CoE-for-Smart-Production/mona/Images/20210218_104930.jpg

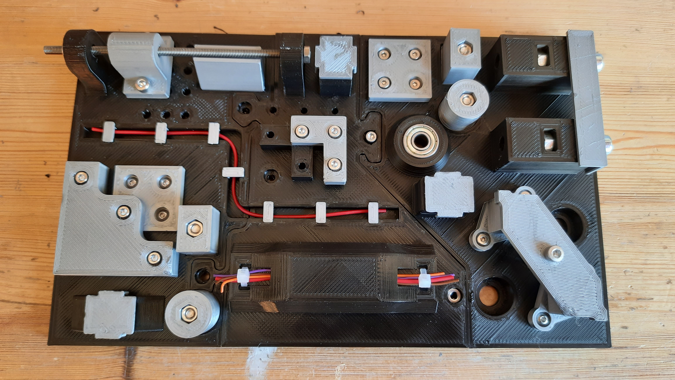
Images/20210218_104930.jpg
