CoE-for-Smart-Production/mona/Models/STL files/BL_Block.stl

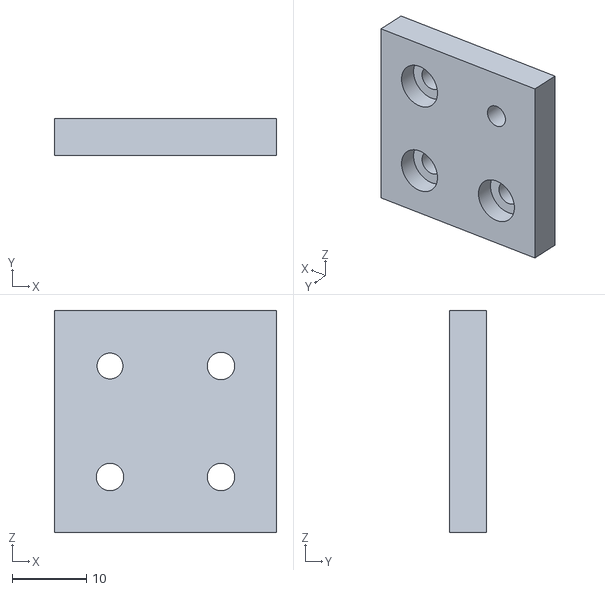
[picture p18: CAD file, 2021-03-04]
Models/STL files/BL_Block.stl
30.0 x 5.00 x 30.0
