CoE-for-Smart-Production/mona/Images/pre_evaluation_assembly.png

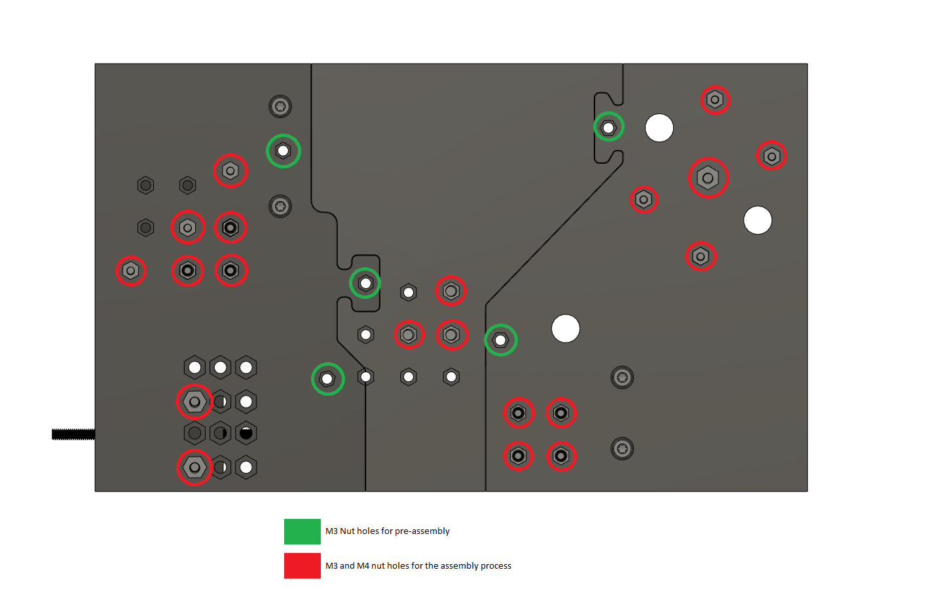
Images/pre_evaluation_assembly.png
