CoE-for-Smart-Production/mona/Images/Workinstruction/AS1_1.png

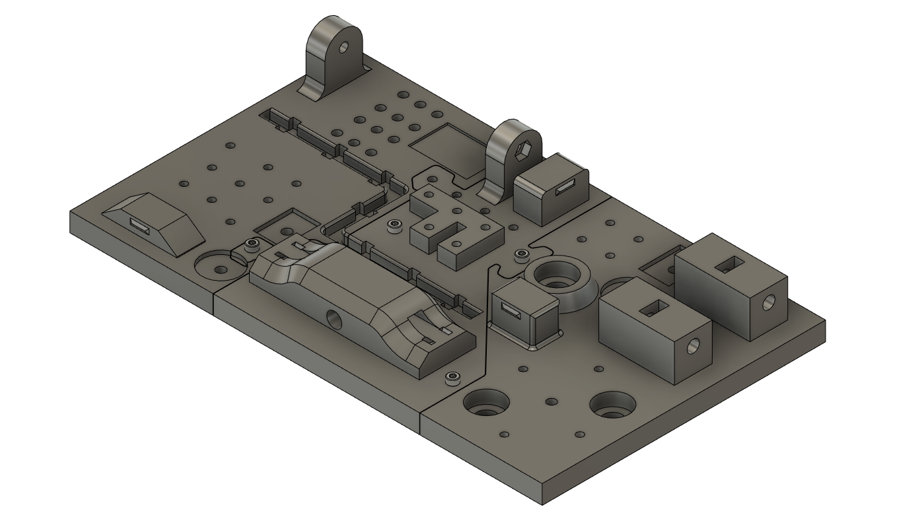
Images/Workinstruction/AS1_1.png
