CoE-for-Smart-Production/mona/Images/Workinstruction/AS2_1.png

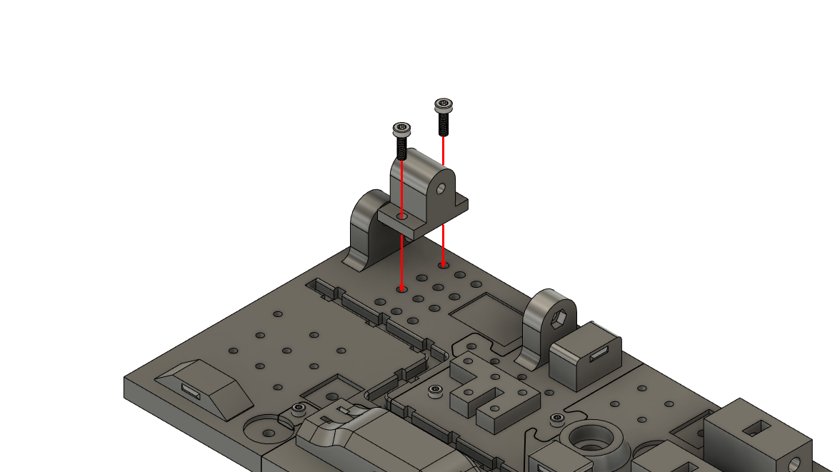
Images/Workinstruction/AS2_1.png
