CoE-for-Smart-Production/mona/Images/Workinstruction/AS2_2.png

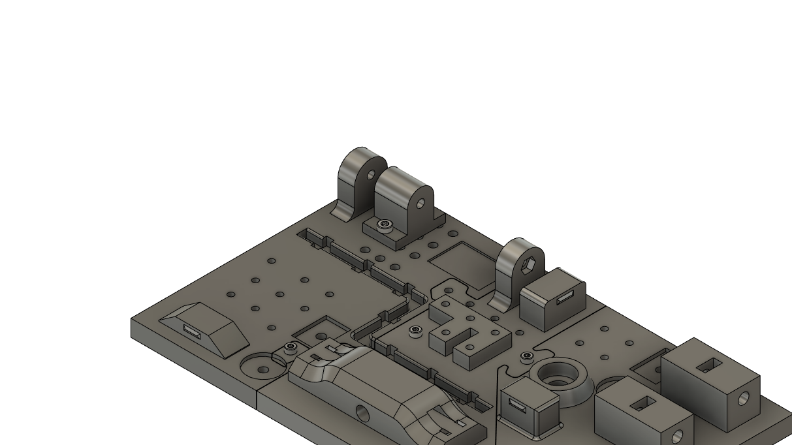
Images/Workinstruction/AS2_2.png
