CoE-for-Smart-Production/mona/Images/Workinstruction/AS3_1.png

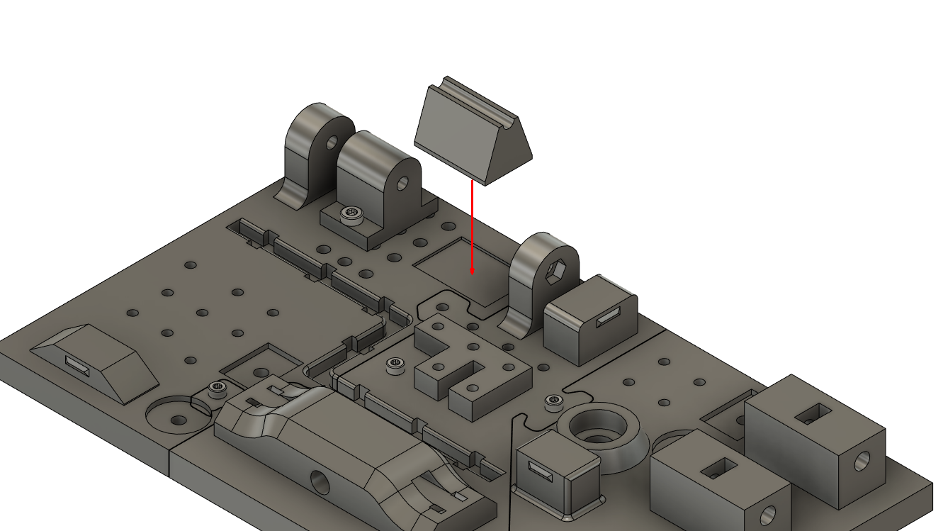
Images/Workinstruction/AS3_1.png
