CoE-for-Smart-Production/mona/Images/Workinstruction/AS3_2.png

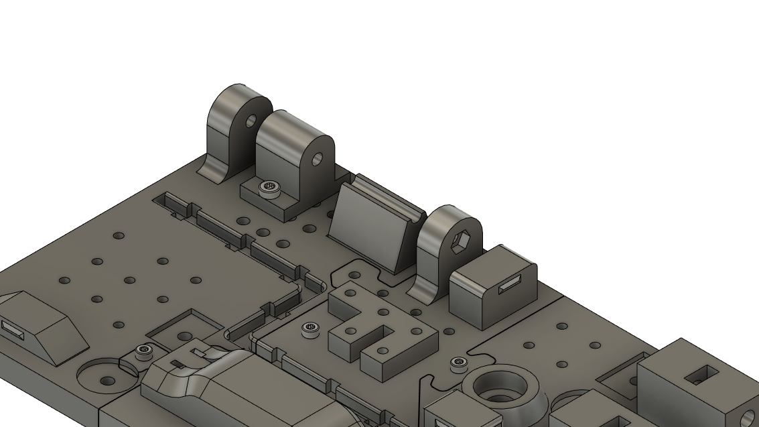
Images/Workinstruction/AS3_2.png
