CoE-for-Smart-Production/mona/Images/Workinstruction/AS4_2.png

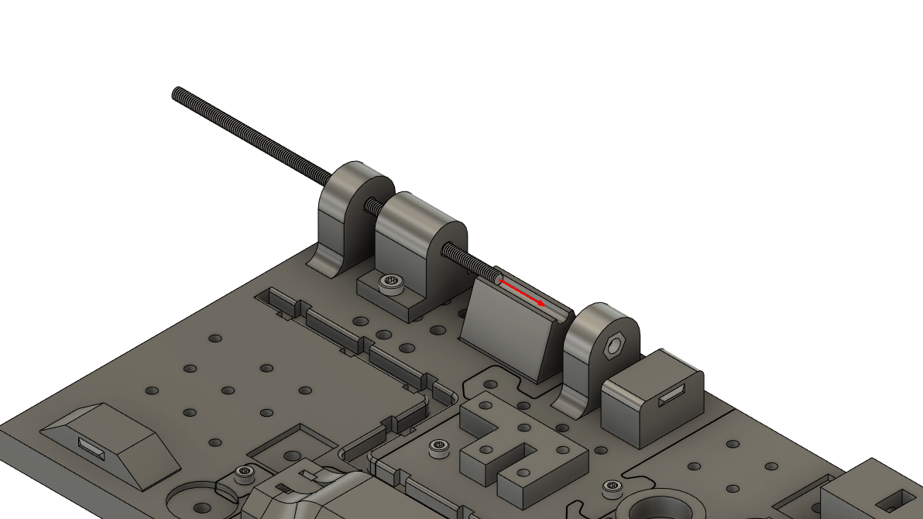
Images/Workinstruction/AS4_2.png
