CoE-for-Smart-Production/mona/Images/Workinstruction/AS4_3.png

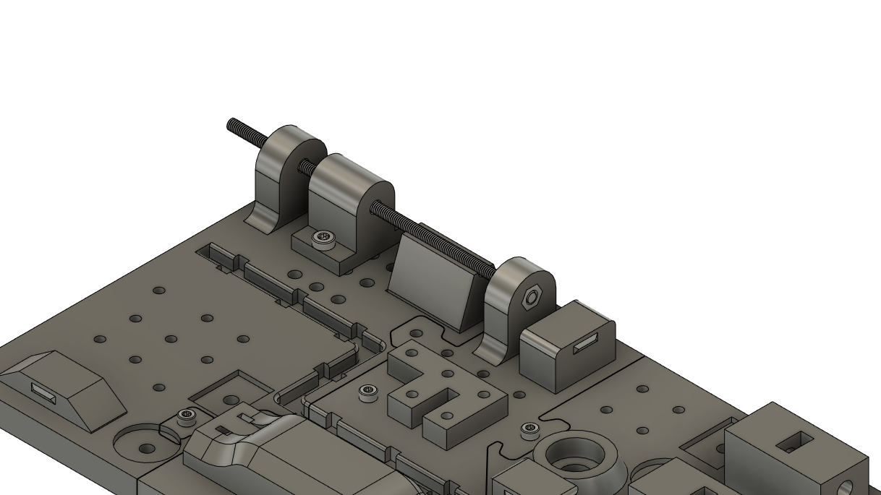
Images/Workinstruction/AS4_3.png
