CoE-for-Smart-Production/mona/Images/Workinstruction/AS5_1.png

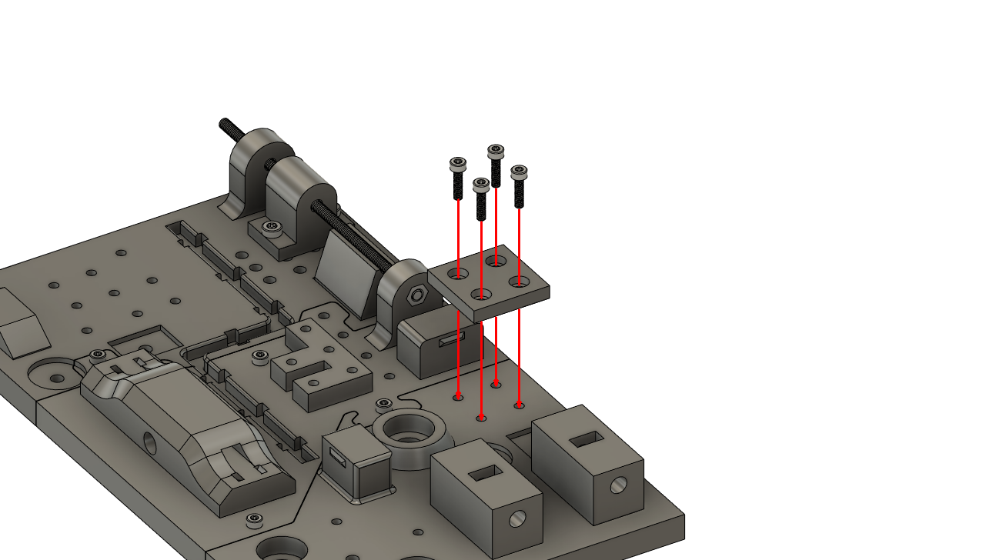
Images/Workinstruction/AS5_1.png
