CoE-for-Smart-Production/mona/Images/Workinstruction/AS5_2.png

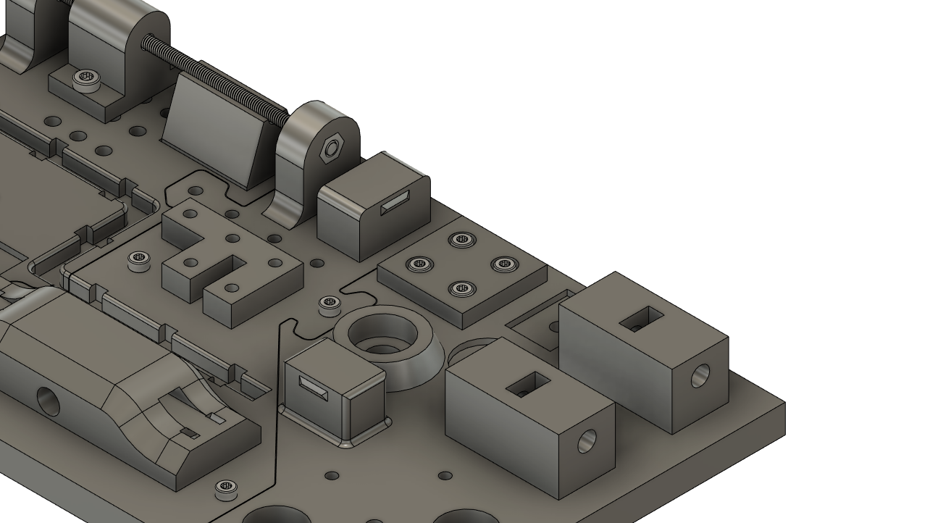
Images/Workinstruction/AS5_2.png
