CoE-for-Smart-Production/mona/Images/Workinstruction/AS6_1.png

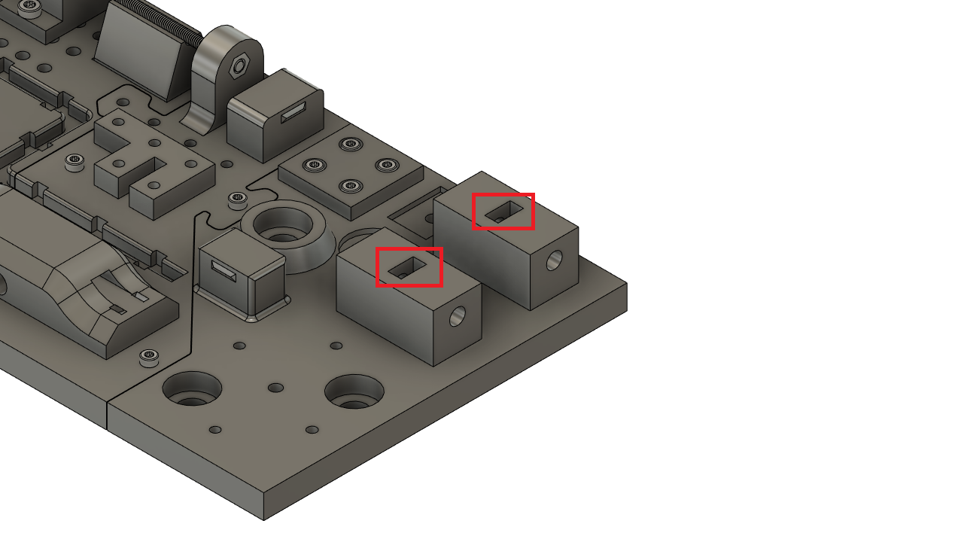
Images/Workinstruction/AS6_1.png
