CoE-for-Smart-Production/mona/Images/Workinstruction/AS6_2.png

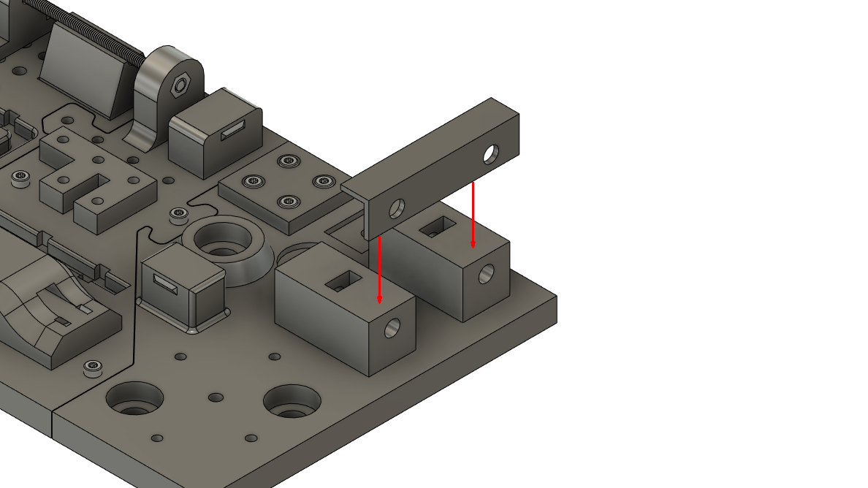
Images/Workinstruction/AS6_2.png
