CoE-for-Smart-Production/mona/Images/Workinstruction/AS6_3.png

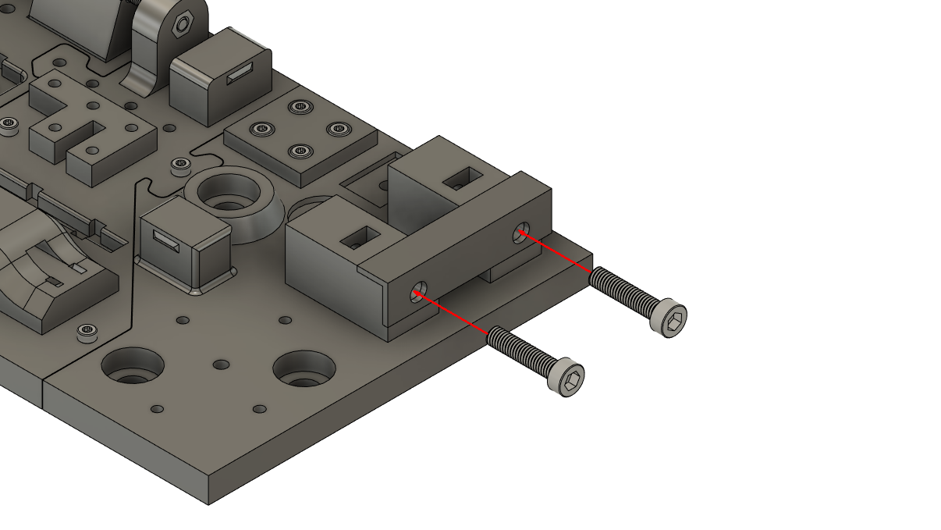
Images/Workinstruction/AS6_3.png
