CoE-for-Smart-Production/mona/Images/Workinstruction/AS7_1.png

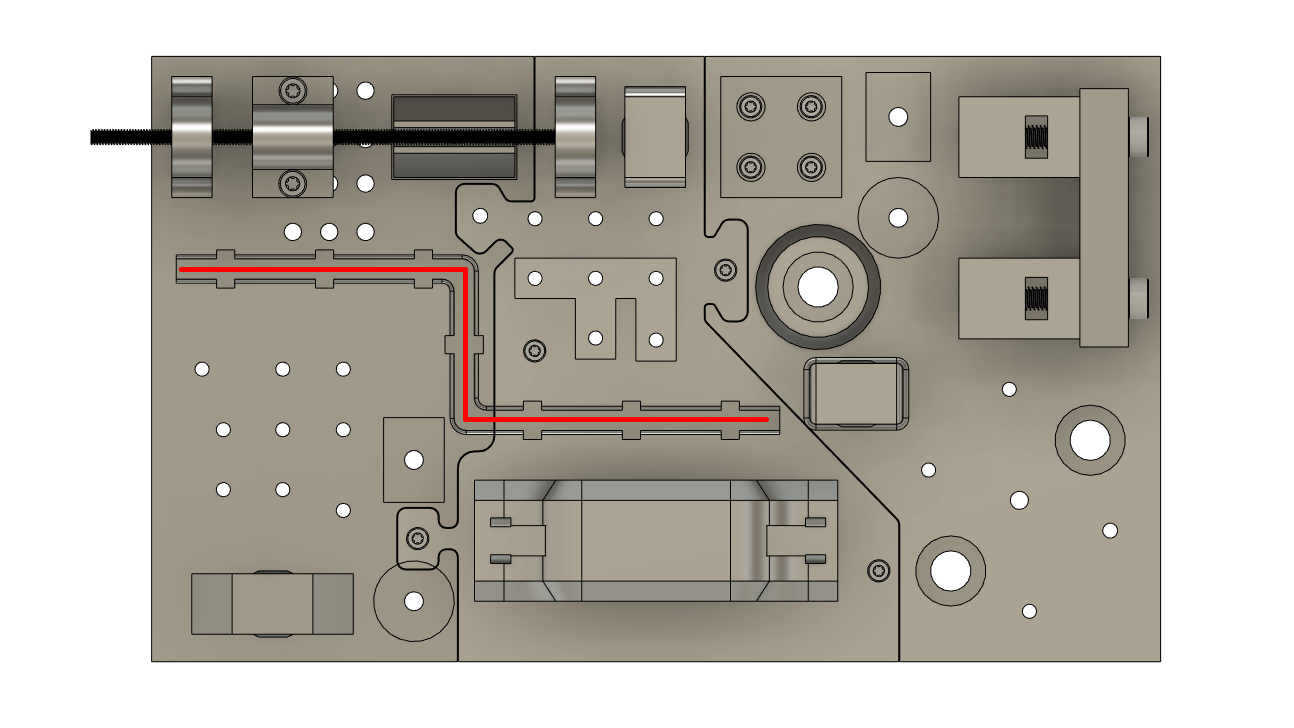
Images/Workinstruction/AS7_1.png
