CoE-for-Smart-Production/mona/Images/Workinstruction/AS7_2.png

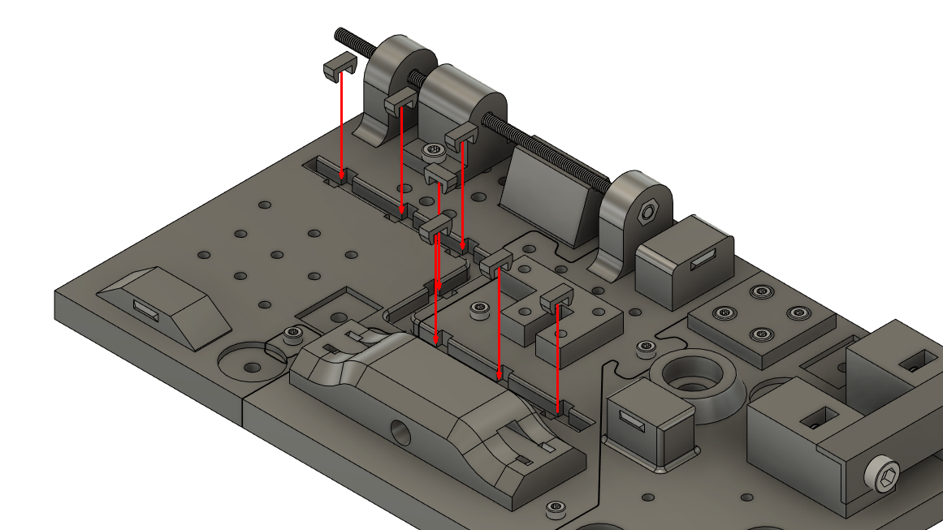
Images/Workinstruction/AS7_2.png
