CoE-for-Smart-Production/mona/Images/Workinstruction/AS7_3.png

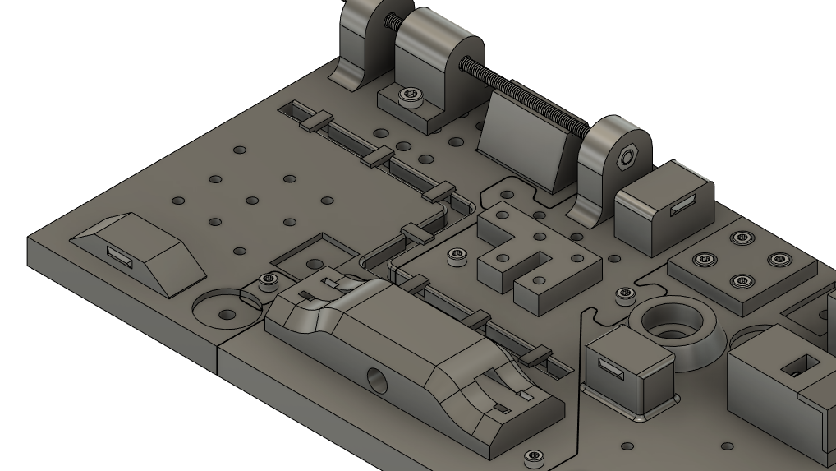
Images/Workinstruction/AS7_3.png
