CoE-for-Smart-Production/mona/Images/Workinstruction/AS8_1.png

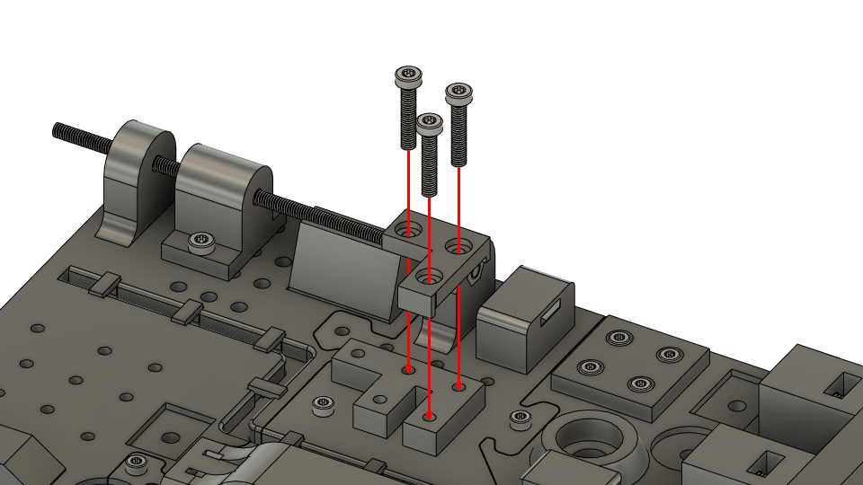
Images/Workinstruction/AS8_1.png
