CoE-for-Smart-Production/mona/Images/Workinstruction/AS8_2.png

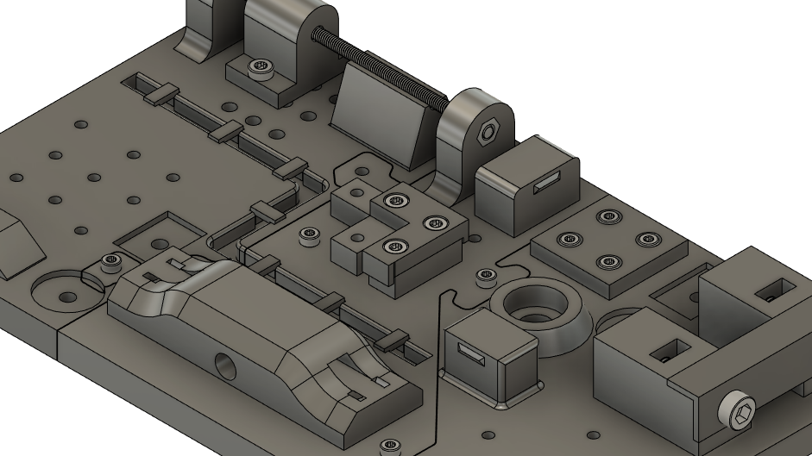
Images/Workinstruction/AS8_2.png
