CoE-for-Smart-Production/mona/Images/Workinstruction/AS9_1.png

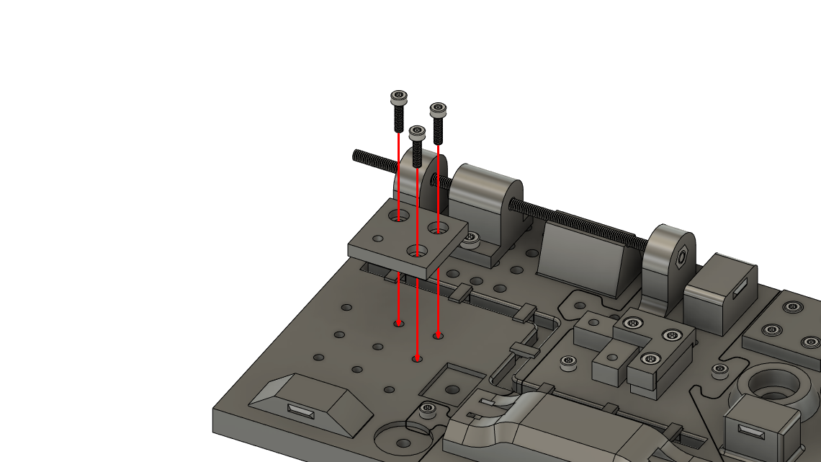
Images/Workinstruction/AS9_1.png
