CoE-for-Smart-Production/mona/Images/Workinstruction/AS9_2.png

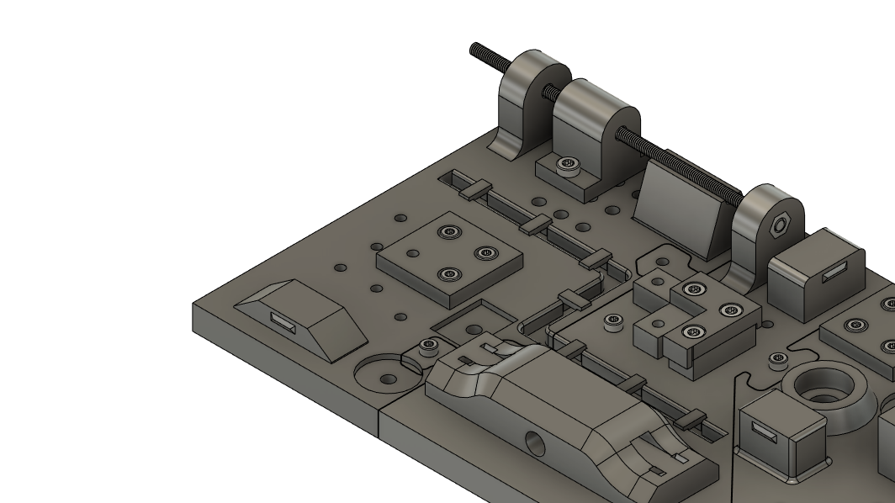
Images/Workinstruction/AS9_2.png
