CoE-for-Smart-Production/mona/Images/Workinstruction/AS10_1.png

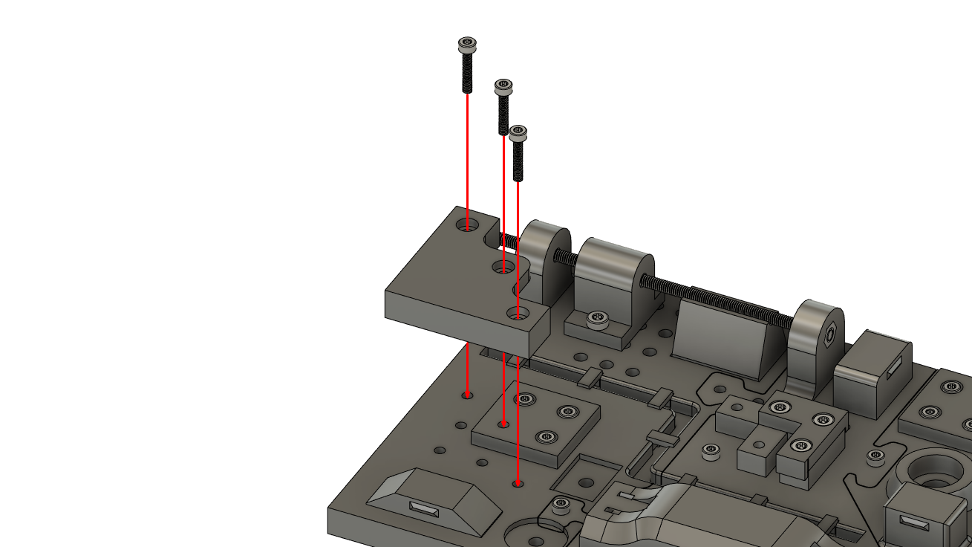
Images/Workinstruction/AS10_1.png
