CoE-for-Smart-Production/mona/Images/Workinstruction/AS10_2.png

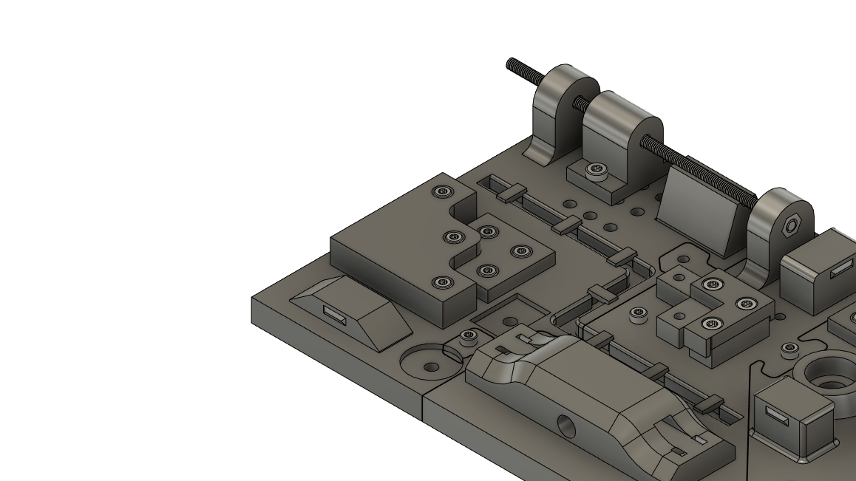
Images/Workinstruction/AS10_2.png
