CoE-for-Smart-Production/mona/Images/Workinstruction/AS11_3.png

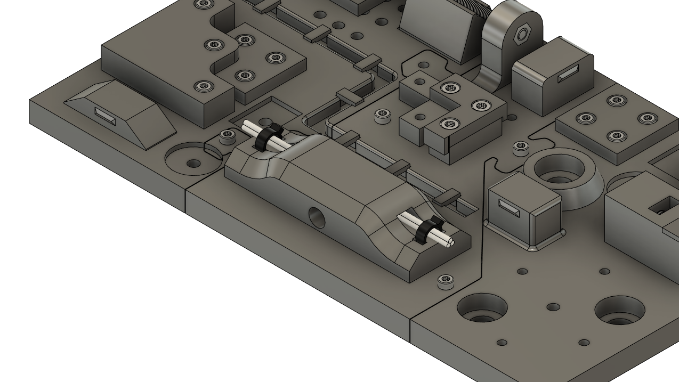
Images/Workinstruction/AS11_3.png
