CoE-for-Smart-Production/mona/Images/Workinstruction/AS12_1.png

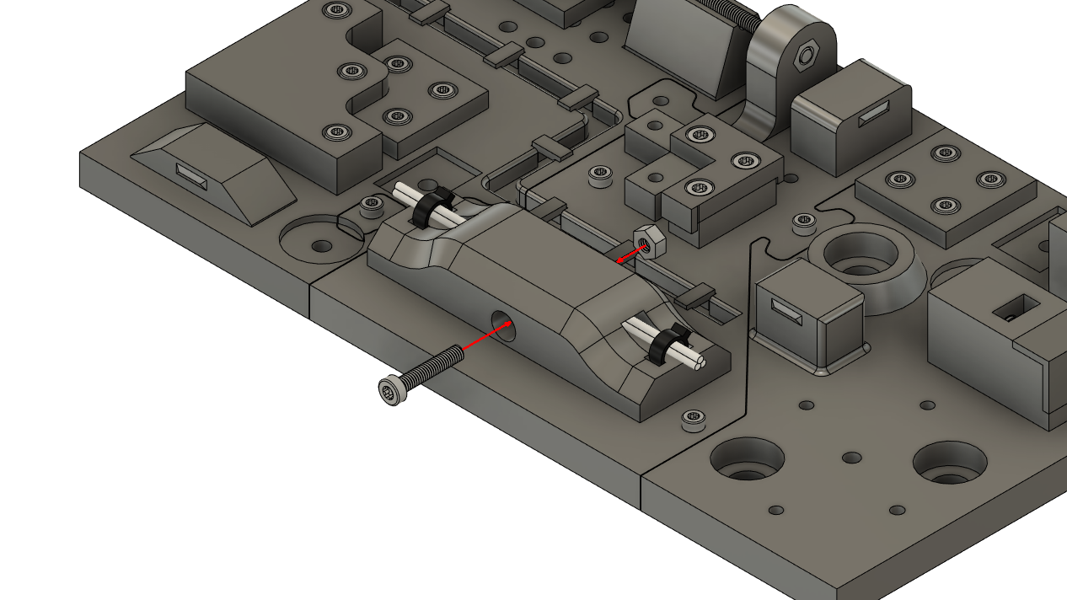
Images/Workinstruction/AS12_1.png
