CoE-for-Smart-Production/mona/Images/Workinstruction/AS12_2.png

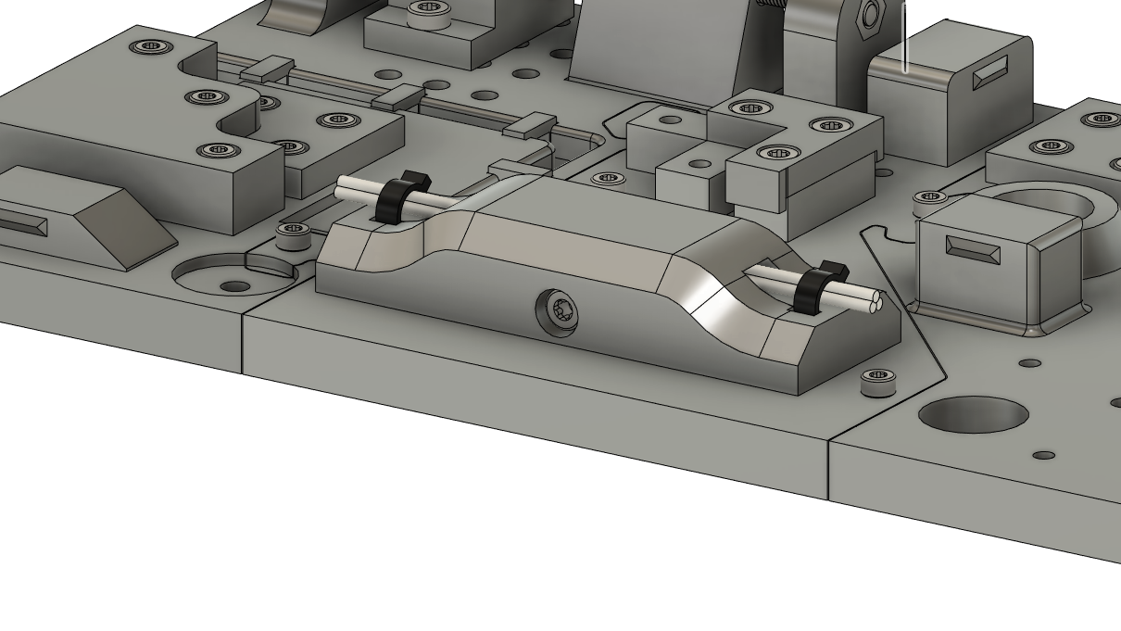
Images/Workinstruction/AS12_2.png
