CoE-for-Smart-Production/mona/Images/Workinstruction/AS13_1.png

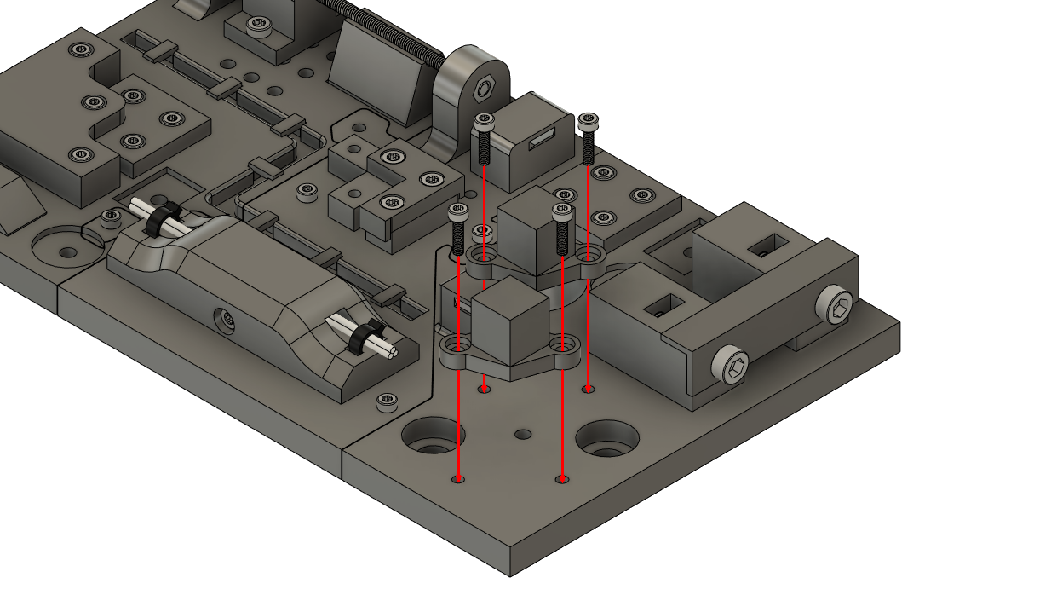
Images/Workinstruction/AS13_1.png
