CoE-for-Smart-Production/mona/Images/Workinstruction/AS13_2.png

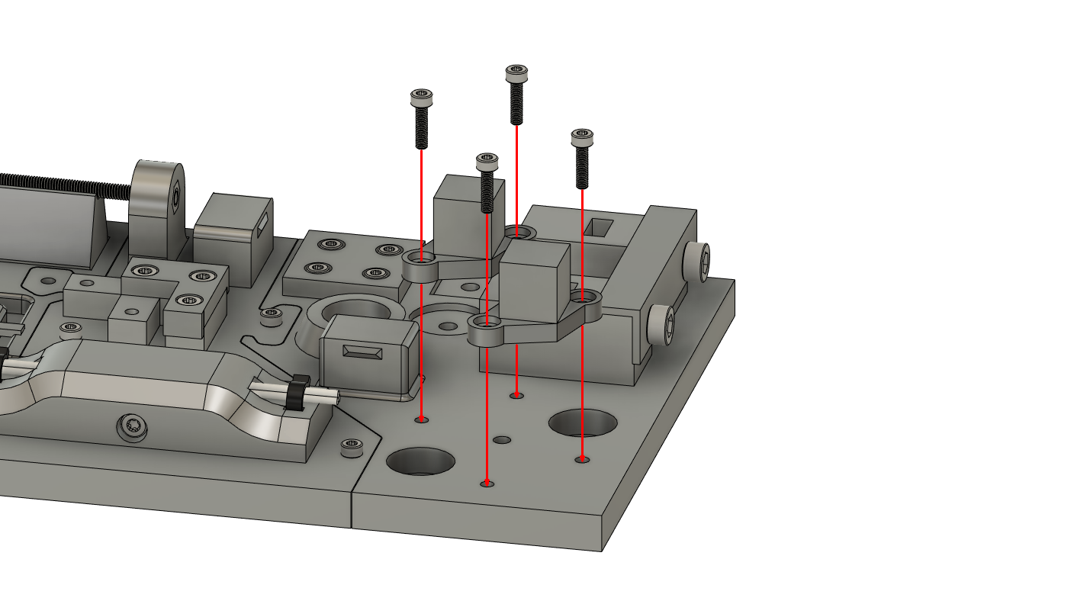
Images/Workinstruction/AS13_2.png
