CoE-for-Smart-Production/mona/Images/Workinstruction/AS13_3.png

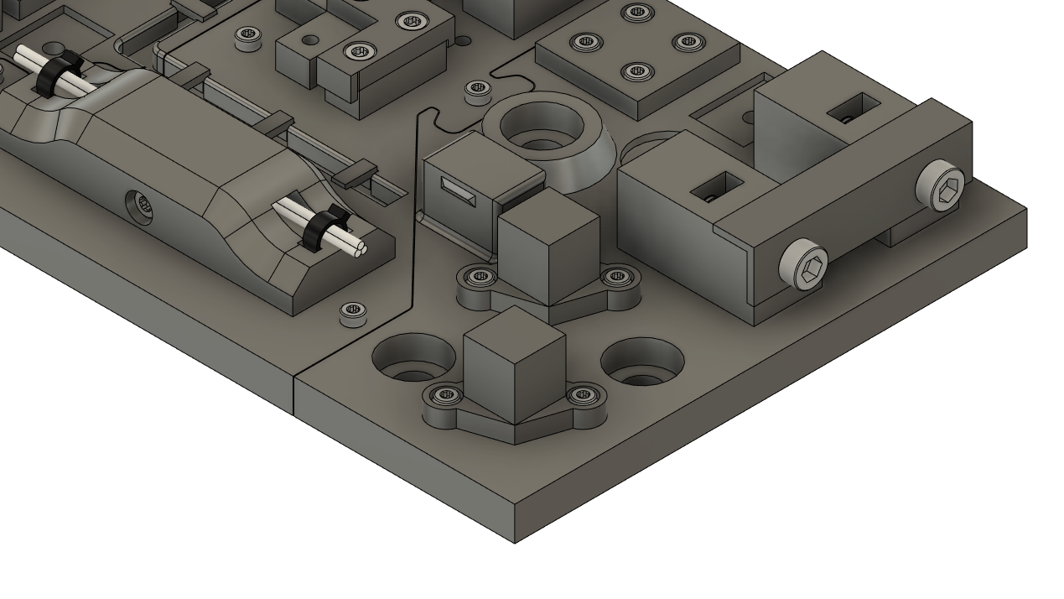
Images/Workinstruction/AS13_3.png
