CoE-for-Smart-Production/mona/Images/Workinstruction/AS14_1.png

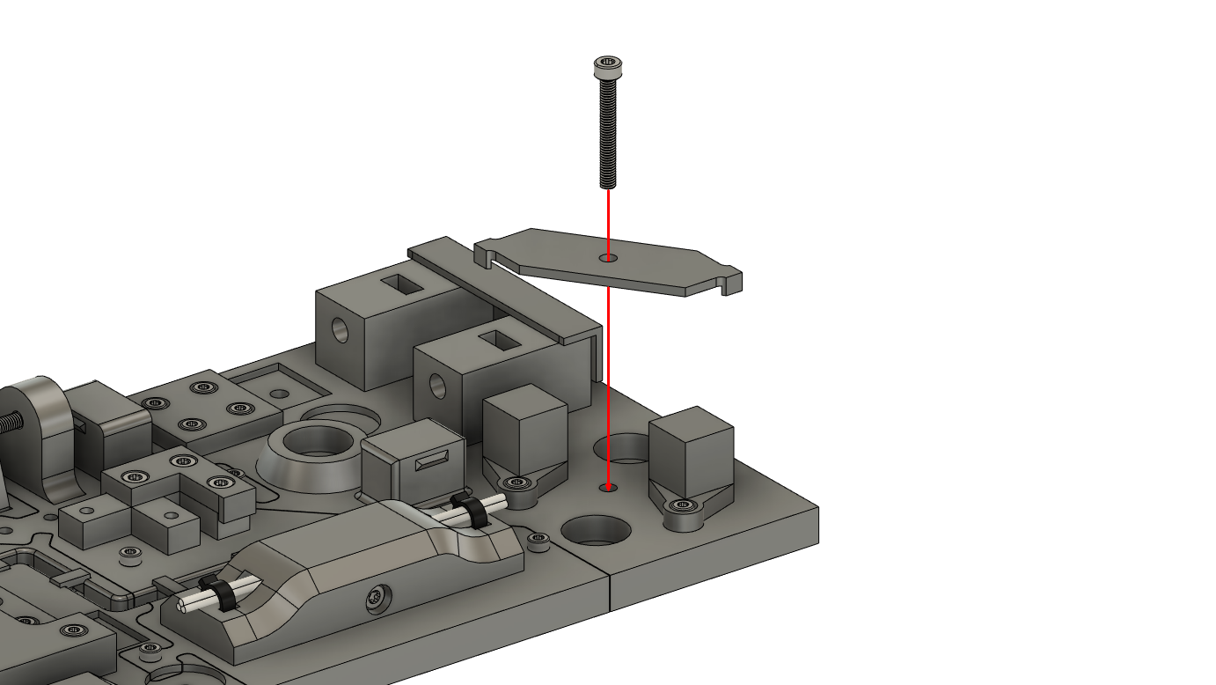
Images/Workinstruction/AS14_1.png
