CoE-for-Smart-Production/mona/Images/Workinstruction/AS15_1.png

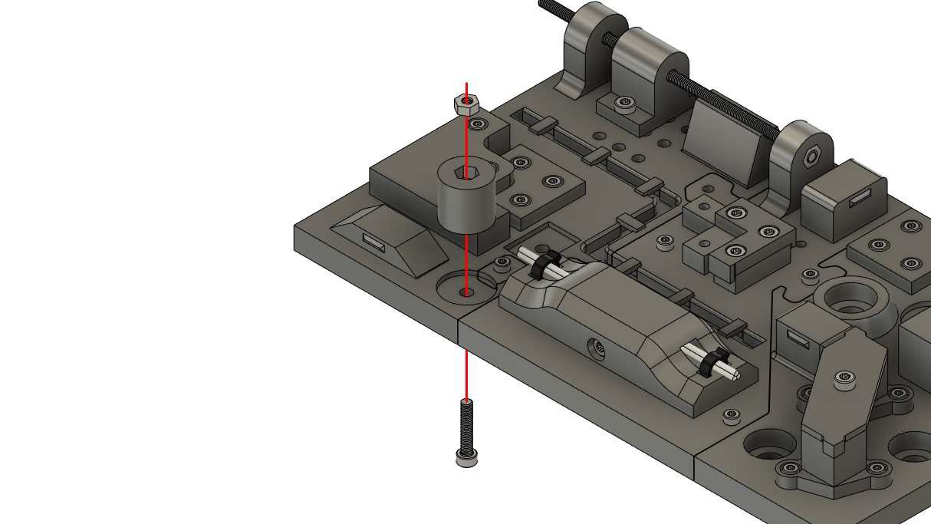
Images/Workinstruction/AS15_1.png
