CoE-for-Smart-Production/mona/Images/Workinstruction/AS15_2.png

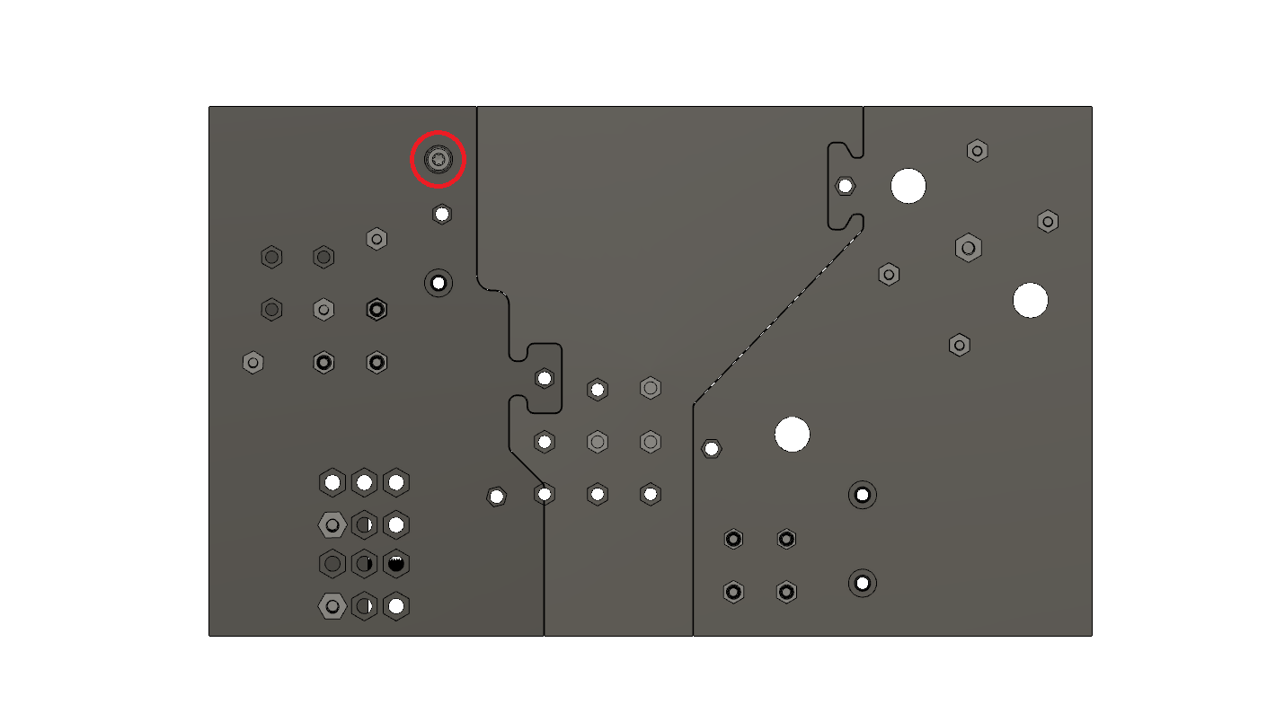
Images/Workinstruction/AS15_2.png
