CoE-for-Smart-Production/mona/Images/Workinstruction/AS15_3.png

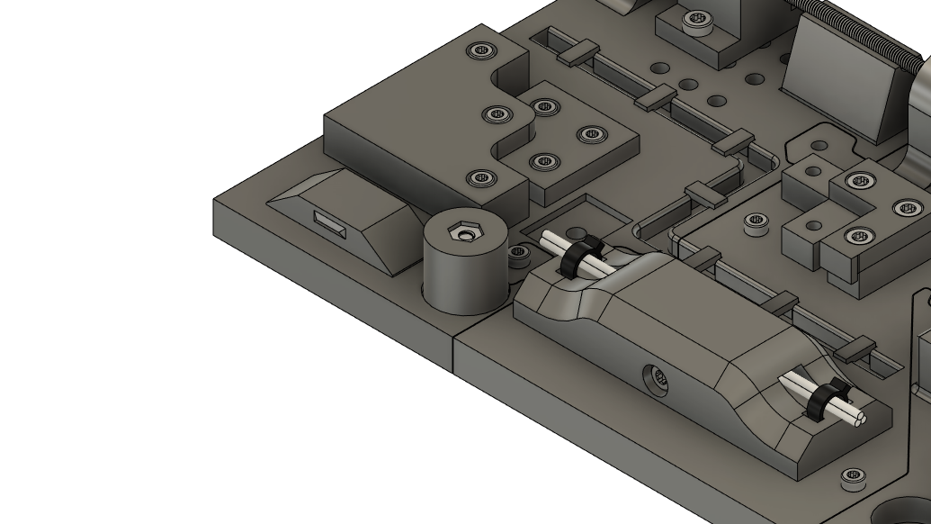
Images/Workinstruction/AS15_3.png
