CoE-for-Smart-Production/mona/Images/Workinstruction/AS16_1.png

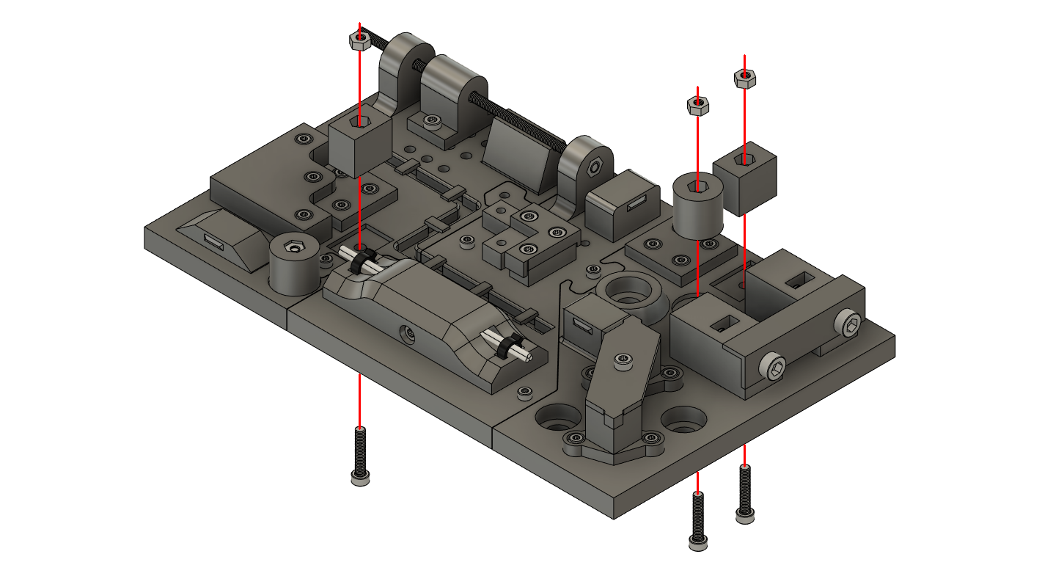
Images/Workinstruction/AS16_1.png
