CoE-for-Smart-Production/mona/Images/Workinstruction/AS16_2.png

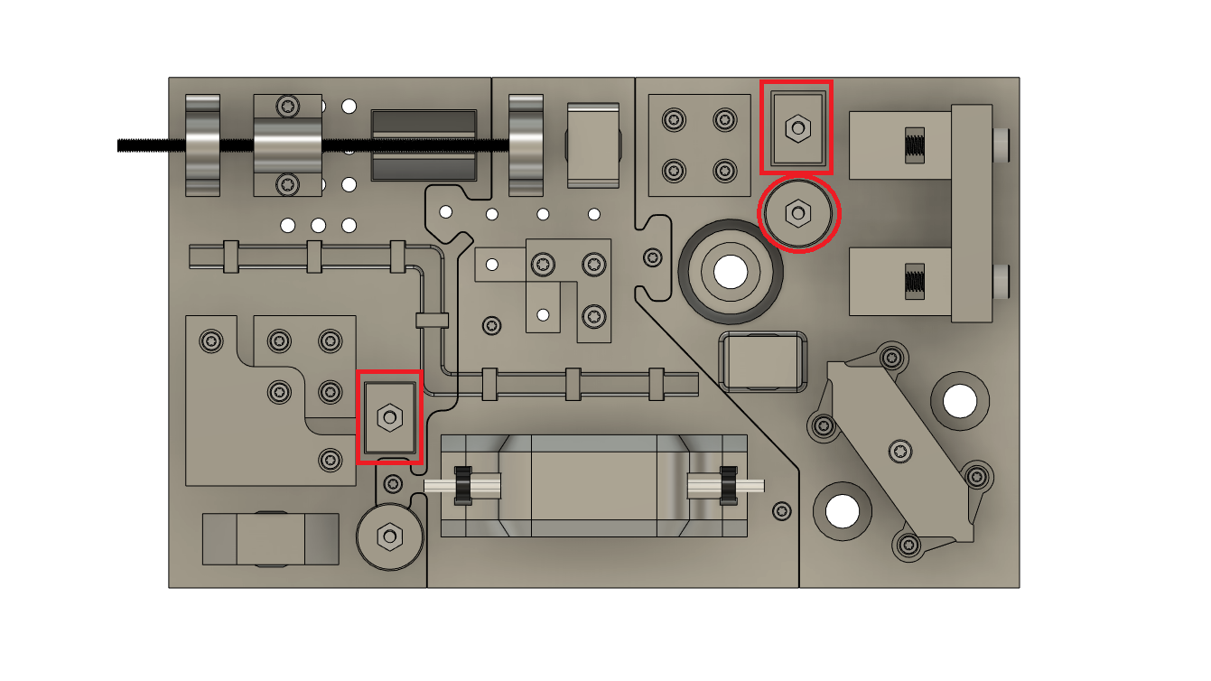
Images/Workinstruction/AS16_2.png
