CoE-for-Smart-Production/mona/Images/Workinstruction/AS16_4.png

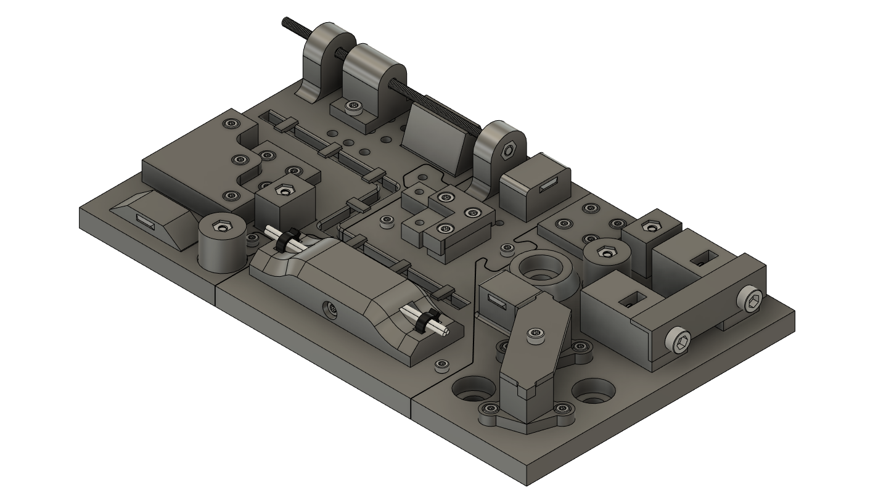
Images/Workinstruction/AS16_4.png
