CoE-for-Smart-Production/mona/Images/Workinstruction/AS17_1.png

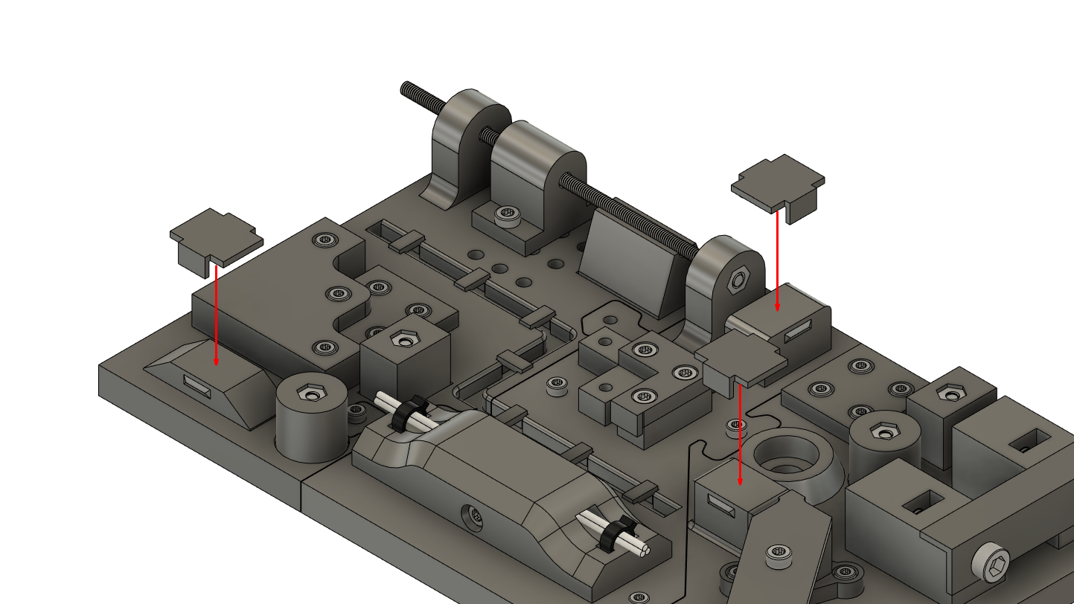
Images/Workinstruction/AS17_1.png
