CoE-for-Smart-Production/mona/Images/Workinstruction/AS18_2.png

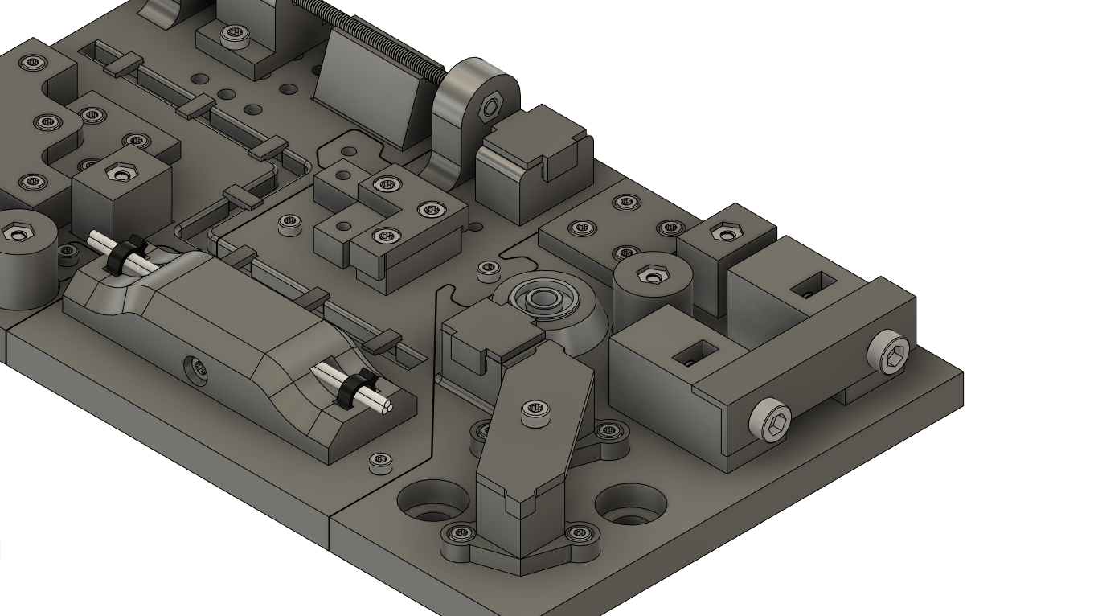
Images/Workinstruction/AS18_2.png
